BasicChaos/Creature/Hardware/Creature v06/Creature v06.kicad_sch

## KiCad design Hardware/Creature v06/Creature v06.kicad_sch (2026-06-21)

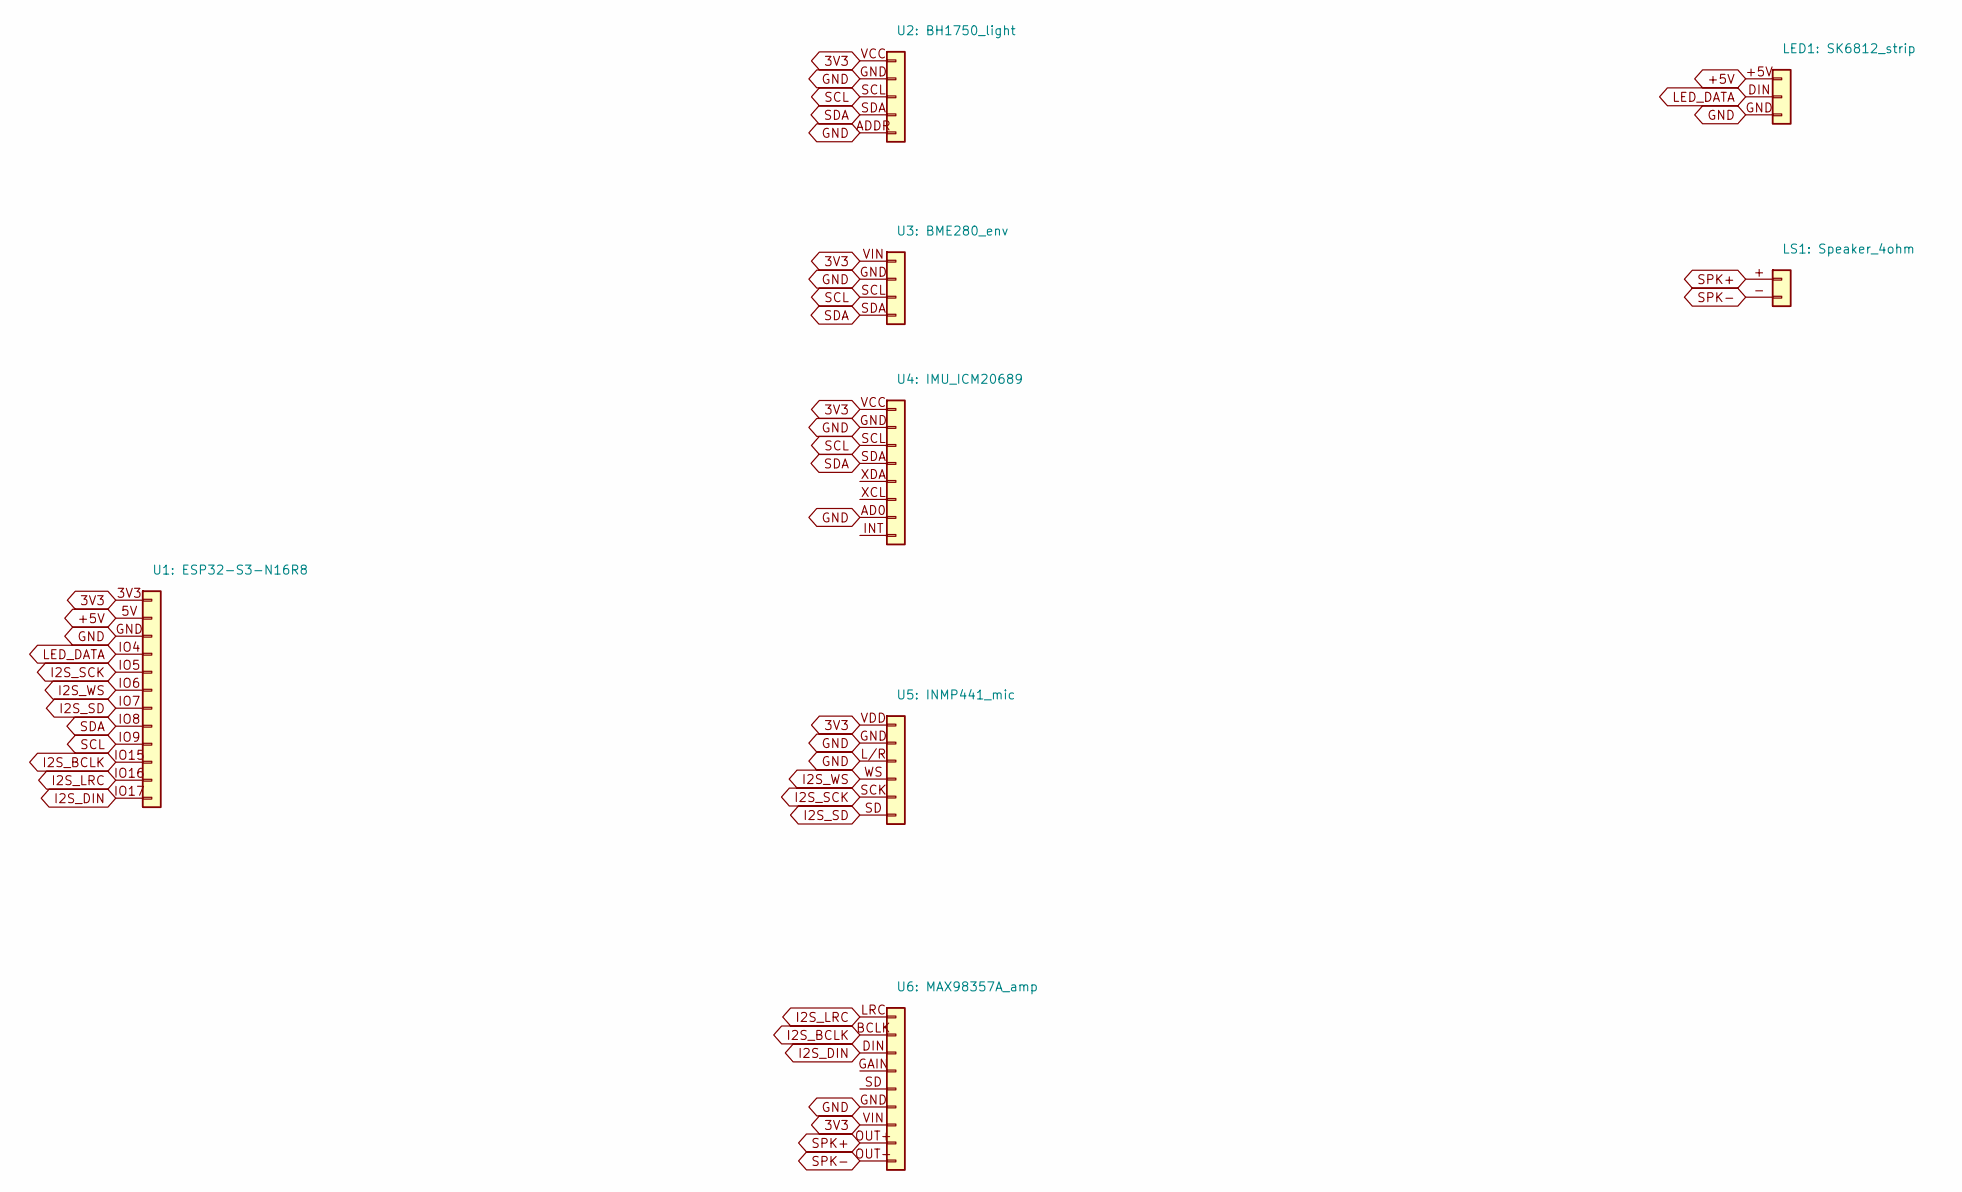
[picture p10: schematic Creature v06.kicad_sch]

Parts:
LED1: SK6812_strip: (no value)
LS1: Speaker_4ohm: (no value)
U1: ESP32-S3-N16R8, U2: BH1750_light, U3: BME280_env, U4: IMU_ICM20689, U5: INMP441_mic, U6: MAX98357A_amp: (no value)

Connections:
3V3: U1: ESP32-S3-N16R8.3V3 (Pin_1), U2: BH1750_light.VCC (Pin_1), U3: BME280_env.VIN (Pin_1), U4: IMU_ICM20689.VCC (Pin_1), U5: INMP441_mic.VDD (Pin_1), U6: MAX98357A_amp.VIN (Pin_7)
+5V: LED1: SK6812_strip.+5V (Pin_1), U1: ESP32-S3-N16R8.5V (Pin_2)
GND: LED1: SK6812_strip.GND (Pin_3), U1: ESP32-S3-N16R8.GND (Pin_3), U2: BH1750_light.ADDR (Pin_5), U2: BH1750_light.GND (Pin_2), U3: BME280_env.GND (Pin_2), U4: IMU_ICM20689.AD0 (Pin_7), U4: IMU_ICM20689.GND (Pin_2), U5: INMP441_mic.GND (Pin_2), U5: INMP441_mic.L/R (Pin_3), U6: MAX98357A_amp.GND (Pin_6)
I2S_BCLK: U1: ESP32-S3-N16R8.IO15 (Pin_10), U6: MAX98357A_amp.BCLK (Pin_2)
I2S_DIN: U1: ESP32-S3-N16R8.IO17 (Pin_12), U6: MAX98357A_amp.DIN (Pin_3)
I2S_LRC: U1: ESP32-S3-N16R8.IO16 (Pin_11), U6: MAX98357A_amp.LRC (Pin_1)
I2S_SCK: U1: ESP32-S3-N16R8.IO5 (Pin_5), U5: INMP441_mic.SCK (Pin_5)
I2S_SD: U1: ESP32-S3-N16R8.IO7 (Pin_7), U5: INMP441_mic.SD (Pin_6)
I2S_WS: U1: ESP32-S3-N16R8.IO6 (Pin_6), U5: INMP441_mic.WS (Pin_4)
LED_DATA: LED1: SK6812_strip.DIN (Pin_2), U1: ESP32-S3-N16R8.IO4 (Pin_4)
SCL: U1: ESP32-S3-N16R8.IO9 (Pin_9), U2: BH1750_light.SCL (Pin_3), U3: BME280_env.SCL (Pin_3), U4: IMU_ICM20689.SCL (Pin_3)
SDA: U1: ESP32-S3-N16R8.IO8 (Pin_8), U2: BH1750_light.SDA (Pin_4), U3: BME280_env.SDA (Pin_4), U4: IMU_ICM20689.SDA (Pin_4)
SPK+: LS1: Speaker_4ohm.+ (Pin_1), U6: MAX98357A_amp.OUT+ (Pin_8)
SPK-: LS1: Speaker_4ohm.- (Pin_2), U6: MAX98357A_amp.OUT- (Pin_9)
